Oscilllator/waveform-generator/rtl/awg/pll_100.v

// diamond 3.7 accepts this PLL
// diamond 3.8-3.9 is untested
// diamond 3.10 or higher is likely to abort with error about unable to use feedback signal
// cause of this could be from wrong CPHASE/FPHASE parameters
module pll_100
(
    input clkin, // 16 MHz, 0 deg
    output clkout0, // 100 MHz, 0 deg
    output locked
);
(* FREQUENCY_PIN_CLKI="16" *)
(* FREQUENCY_PIN_CLKOP="100" *)
(* ICP_CURRENT="12" *) (* LPF_RESISTOR="8" *) (* MFG_ENABLE_FILTEROPAMP="1" *) (* MFG_GMCREF_SEL="2" *)
EHXPLLL #(
        .PLLRST_ENA("DISABLED"),
        .INTFB_WAKE("DISABLED"),
        .STDBY_ENABLE("DISABLED"),
        .DPHASE_SOURCE("DISABLED"),
        .OUTDIVIDER_MUXA("DIVA"),
        .OUTDIVIDER_MUXB("DIVB"),
        .OUTDIVIDER_MUXC("DIVC"),
        .OUTDIVIDER_MUXD("DIVD"),
        .CLKI_DIV(4),
        .CLKOP_ENABLE("ENABLED"),
        .CLKOP_DIV(6),
        .CLKOP_CPHASE(2),
        .CLKOP_FPHASE(0),
        .FEEDBK_PATH("CLKOP"),
        .CLKFB_DIV(25)
    ) pll_i (
        .RST(1'b0),
        .STDBY(1'b0),
        .CLKI(clkin),
        .CLKOP(clkout0),
        .CLKFB(clkout0),
        .CLKINTFB(),
        .PHASESEL0(1'b0),
        .PHASESEL1(1'b0),
        .PHASEDIR(1'b1),
        .PHASESTEP(1'b1),
        .PHASELOADREG(1'b1),
        .PLLWAKESYNC(1'b0),
        .ENCLKOP(1'b0),
        .LOCK(locked)
	);
endmodule
